lata-mas/DTHIS-C_JoseRra/Diagramas/Esquematicos/pt1000_esquematico.png

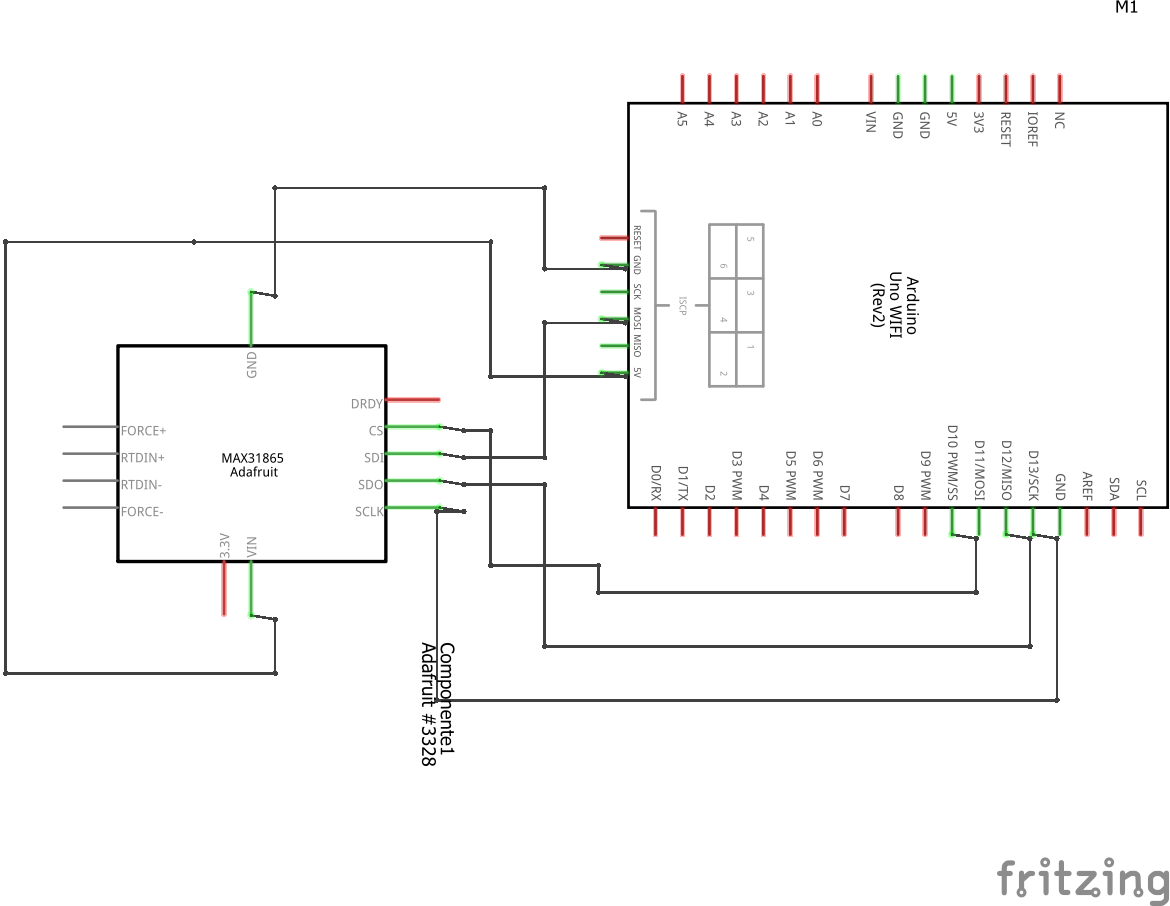
Diagramas/Esquematicos/pt1000_esquematico.png
