lata-mas/DTHIS-C_JoseRra/Diagramas/Pictogramas/diagrama_bloques.png

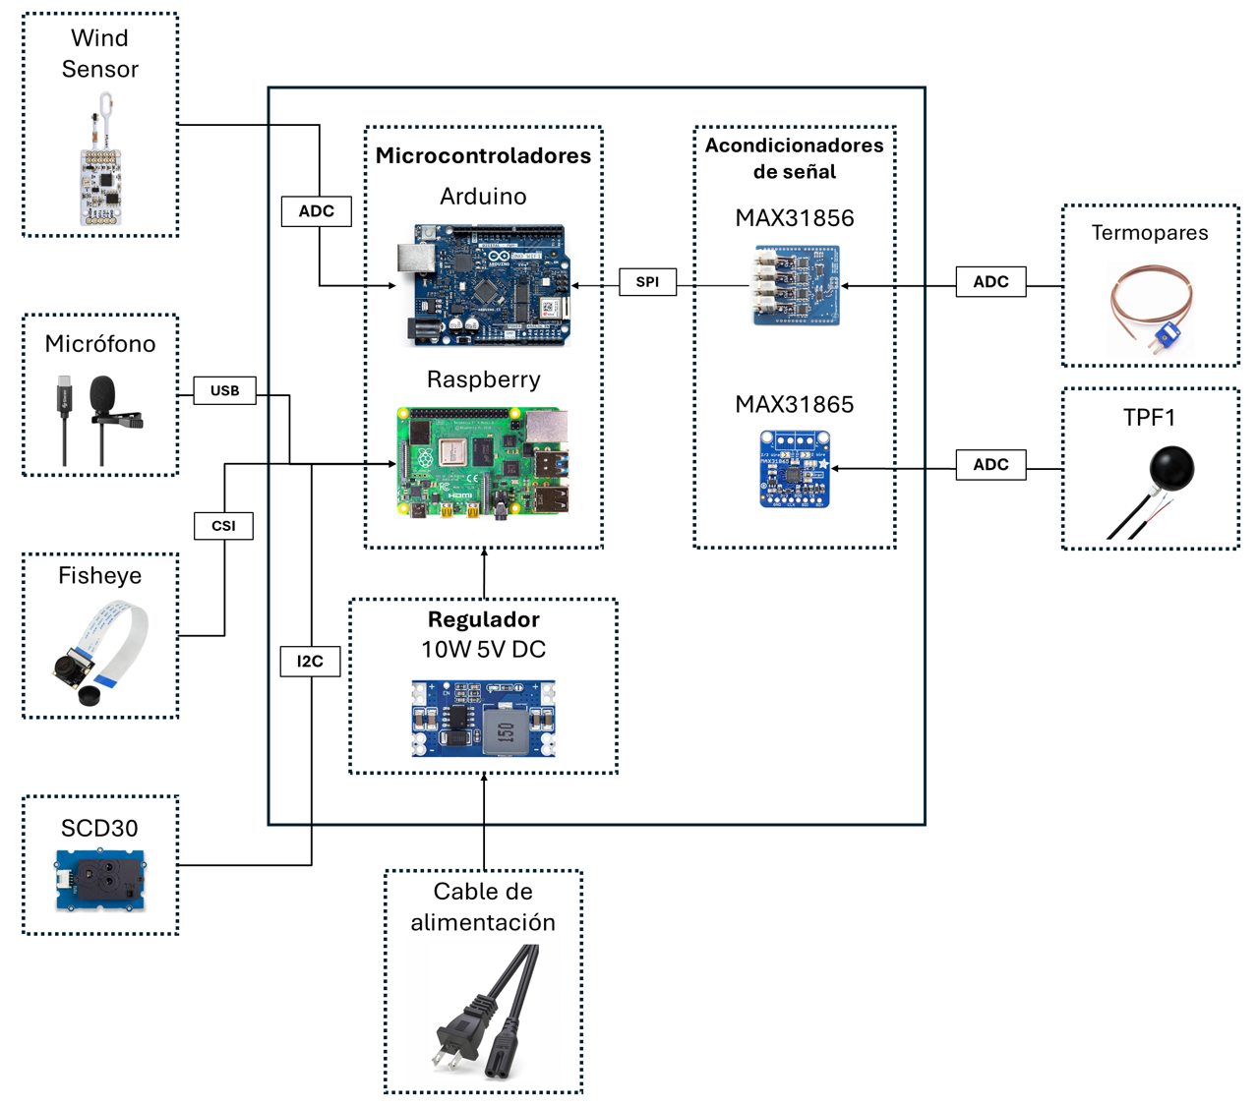
Diagramas/Pictogramas/diagrama_bloques.png
