lata-mas/DTHIS-C_JoseRra/Diagramas/Pictogramas/micro_bb.png

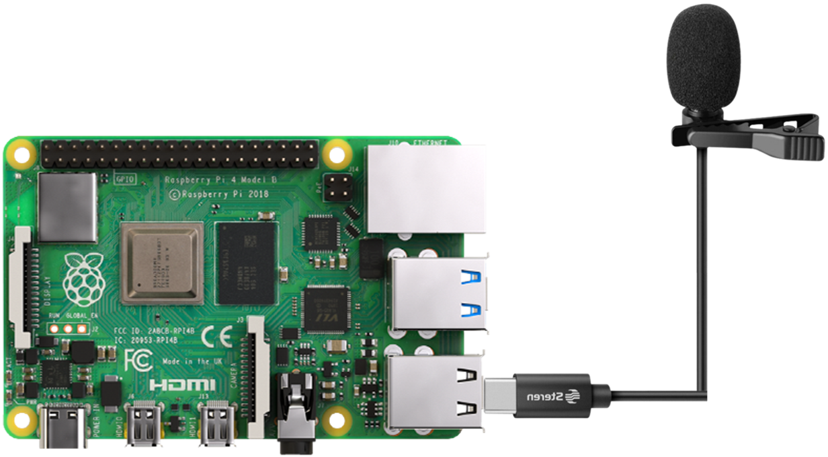
Diagramas/Pictogramas/micro_bb.png
