lata-mas/DTHIS-C_JoseRra/CAD/STEP/Wind_Sensor/WS_Case.step

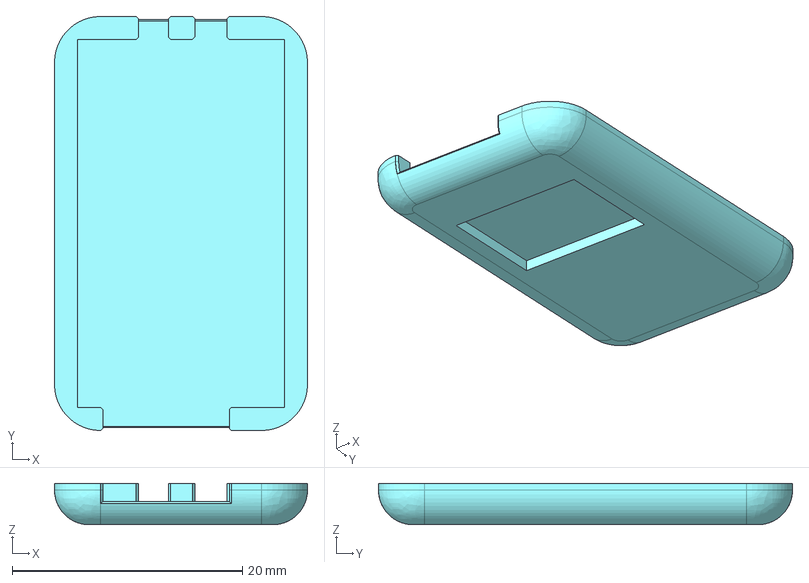
[picture p24: CAD file, 2025-07-02]
CAD/STEP/Wind_Sensor/WS_Case.step
22.0 x 36.0 x 3.60 mm
