lata-mas/DTHIS-C_JoseRra/CAD/STEP/Case/Cover.step

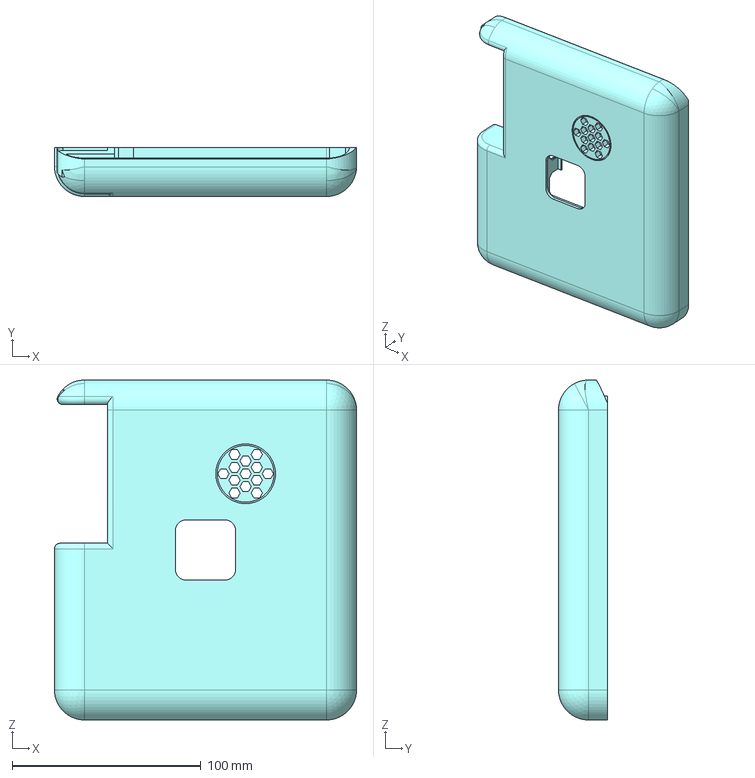
[picture p25: CAD file, 2025-07-02]
CAD/STEP/Case/Cover.step
160.0 x 26.0 x 180.0 mm
