lata-mas/DTHIS-C_JoseRra/Scripts/Arduino/main/Termopares.ino

#include <PWFusion_MAX31856.h>

// Definición de los pines chip select para cada termopar
uint8_t tcChipSelects[] = {10, 9, 8, 7};
#define NUM_THERMOCOUPLES   (sizeof(tcChipSelects) / sizeof(uint8_t))

// Coeficientes de calibración para cada termopar
const float m[NUM_THERMOCOUPLES] = {1.0450, 1.0602, 1.0814, 1.0554};  // Pendientes
const float b[NUM_THERMOCOUPLES] = {-2.4327, -2.8632, -4.4316, -3.9348};  // Intersecciones

// Se crea un objeto MAX31856 para cada termopar
MAX31856 thermocouples[NUM_THERMOCOUPLES];

float* ThermocoupleTemp() {
  static float tc_temps[NUM_THERMOCOUPLES];
  static bool initialized = false;

  // Inicializa los sensores solo la primera vez que se llama a la función
  if (!initialized) {
    delay(1000);  // Espera para la estabilización de los sensores
    for (int i = 0; i < NUM_THERMOCOUPLES; i++) {
      thermocouples[i].begin(tcChipSelects[i]);
      thermocouples[i].config(T_TYPE, CUTOFF_60HZ, AVG_SEL_4SAMP, CMODE_OFF);
    }
    initialized = true;
  }
  
  // Inicia la medición en cada sensor
  for (int i = 0; i < NUM_THERMOCOUPLES; i++) {
    thermocouples[i].startOneShotMeasurement();
  }
  
  // Espera el tiempo necesario para que la conversión se complete
  delay(180);
  
  // Actualiza la muestra en cada sensor
  for (int i = 0; i < NUM_THERMOCOUPLES; i++) {
    thermocouples[i].sample();
  }
  
  // Obtiene la temperatura ambiente de cada sensor y aplica la calibración
  for (int i = 0; i < NUM_THERMOCOUPLES; i++) {
    if (thermocouples[i].getStatus() != 0) {
      // En caso de error, se asigna NaN (Not a Number)
      tc_temps[i] = NAN;
    } else {
      float raw_temperature = thermocouples[i].getTemperature();
      tc_temps[i] = m[i] * raw_temperature + b[i];  // Aplica la calibración
    }
  }
  
  return tc_temps;
}
